0XIAOMAO0/CWU_LED/software/CWU_LED/project/inc/cct_to_cie.h

#ifndef CCT_TO_CIE_H
#define CCT_TO_CIE_H

#define CCT_MIN 2500
#define CCT_MAX 6500

#define CCT_RANGE (CCT_MAX - CCT_MIN)
// This file is used to convert CCT to CIE color space.
// The CCT range is 2500K-6500K.
const float CIE_ARRY[][2] ={
{0.476993298233858,	0.413675289942435}, // 2500k	
{0.476099925127525,	0.413553952226202}, // 2510k	
{0.475210446423188,	0.413428827337877}, // 2520k	
{0.474324856106916,	0.413299979486579}, // 2530k	
{0.473443147918802,	0.413167472190078}, // 2540k	
{0.472565315357245,	0.413031368275923}, // 2550k	
{0.471691351683258,	0.412891729882807}, // 2560k	
{0.470821249924792,	0.412748618462133}, // 2570k	
{0.469955002881062,	0.412602094779799}, // 2580k	
{0.469092603126886,	0.412452218918178}, // 2590k	
{0.468234043017033,	0.412299050278290}, // 2600k	
{0.467379314690560,	0.412142647582159}, // 2610k	
{0.466528410075157,	0.411983068875347}, // 2620k	
{0.465681320891482,	0.411820371529656}, // 2630k	
{0.464838038657489,	0.411654612245991}, // 2640k	
{0.463998554692746,	0.411485847057383}, // 2650k	
{0.463162860122743,	0.411314131332149}, // 2660k	
{0.462330945883173,	0.411139519777208}, // 2670k	
{0.461502802724214,	0.410962066441520}, // 2680k	
{0.460678421214773,	0.410781824719658}, // 2690k	
{0.459857791746717,	0.410598847355503}, // 2700k	
{0.459040904539081,	0.410413186446054}, // 2710k	
{0.458227749642249,	0.410224893445347}, // 2720k	
{0.457418316942099,	0.410034019168485}, // 2730k	
{0.456612596164132,	0.409840613795755}, // 2740k	
{0.455810576877562,	0.409644726876854}, // 2750k	
{0.455012248499377,	0.409446407335191}, // 2760k	
{0.454217600298360,	0.409245703472280}, // 2770k	
{0.453426621399085,	0.409042662972206}, // 2780k	
{0.452639300785869,	0.408837332906172}, // 2790k	
{0.451855627306685,	0.408629759737106}, // 2800k	
{0.451075589677048,	0.408419989324343}, // 2810k	
{0.450299176483844,	0.408208066928357}, // 2820k	
{0.449526376189136,	0.407994037215556}, // 2830k	
{0.448757177133914,	0.407777944263126}, // 2840k	
{0.447991567541816,	0.407559831563923}, // 2850k	
{0.447229535522791,	0.407339742031414}, // 2860k	
{0.446471069076735,	0.407117718004646}, // 2870k	
{0.445716156097067,	0.406893801253269}, // 2880k	
{0.444964784374273,	0.406668032982576}, // 2890k	
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
};



#endif
