0XIAOMAO0/CWU_LED/software/CWU_LED/project/src/at32f421_int.c

/* add user code begin Header */
/**
  **************************************************************************
  * @file     at32f421_int.c
  * @brief    main interrupt service routines.
  **************************************************************************
  *                       Copyright notice & Disclaimer
  *
  * The software Board Support Package (BSP) that is made available to
  * download from Artery official website is the copyrighted work of Artery.
  * Artery authorizes customers to use, copy, and distribute the BSP
  * software and its related documentation for the purpose of design and
  * development in conjunction with Artery microcontrollers. Use of the
  * software is governed by this copyright notice and the following disclaimer.
  *
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
  **************************************************************************
  */
/* add user code end Header */

/* includes ------------------------------------------------------------------*/
#include "at32f421_int.h"

/* private includes ----------------------------------------------------------*/
/* add user code begin private includes */
#include "at32f421_wk_config.h"
/* add user code end private includes */

/* private typedef -----------------------------------------------------------*/
/* add user code begin private typedef */

/* add user code end private typedef */

/* private define ------------------------------------------------------------*/
/* add user code begin private define */

/* add user code end private define */

/* private macro -------------------------------------------------------------*/
/* add user code begin private macro */

/* add user code end private macro */

/* private variables ---------------------------------------------------------*/
/* add user code begin private variables */

/* add user code end private variables */

/* private function prototypes --------------------------------------------*/
/* add user code begin function prototypes */

/* add user code end function prototypes */

/* private user code ---------------------------------------------------------*/
/* add user code begin 0 */

/* add user code end 0 */

/* external variables ---------------------------------------------------------*/
/* add user code begin external variables */

/* add user code end external variables */

/**
  * @brief  this function handles nmi exception.
  * @param  none
  * @retval none
  */
void NMI_Handler(void)
{
  /* add user code begin NonMaskableInt_IRQ 0 */

  /* add user code end NonMaskableInt_IRQ 0 */

  /* add user code begin NonMaskableInt_IRQ 1 */

  /* add user code end NonMaskableInt_IRQ 1 */
}

/**
  * @brief  this function handles hard fault exception.
  * @param  none
  * @retval none
  */
void HardFault_Handler(void)
{
  /* add user code begin HardFault_IRQ 0 */

  /* add user code end HardFault_IRQ 0 */
  /* go to infinite loop when hard fault exception occurs */
  while (1)
  {
    /* add user code begin W1_HardFault_IRQ 0 */

    /* add user code end W1_HardFault_IRQ 0 */
  }
}

/**
  * @brief  this function handles memory manage exception.
  * @param  none
  * @retval none
  */
void MemManage_Handler(void)
{
  /* add user code begin MemoryManagement_IRQ 0 */

  /* add user code end MemoryManagement_IRQ 0 */
  /* go to infinite loop when memory manage exception occurs */
  while (1)
  {
    /* add user code begin W1_MemoryManagement_IRQ 0 */

    /* add user code end W1_MemoryManagement_IRQ 0 */
  }
}

/**
  * @brief  this function handles bus fault exception.
  * @param  none
  * @retval none
  */
void BusFault_Handler(void)
{
  /* add user code begin BusFault_IRQ 0 */

  /* add user code end BusFault_IRQ 0 */
  /* go to infinite loop when bus fault exception occurs */
  while (1)
  {
    /* add user code begin W1_BusFault_IRQ 0 */

    /* add user code end W1_BusFault_IRQ 0 */
  }
}

/**
  * @brief  this function handles usage fault exception.
  * @param  none
  * @retval none
  */
void UsageFault_Handler(void)
{
  /* add user code begin UsageFault_IRQ 0 */

  /* add user code end UsageFault_IRQ 0 */
  /* go to infinite loop when usage fault exception occurs */
  while (1)
  {
    /* add user code begin W1_UsageFault_IRQ 0 */

    /* add user code end W1_UsageFault_IRQ 0 */
  }
}

/**
  * @brief  this function handles svcall exception.
  * @param  none
  * @retval none
  */
void SVC_Handler(void)
{
  /* add user code begin SVCall_IRQ 0 */

  /* add user code end SVCall_IRQ 0 */
  /* add user code begin SVCall_IRQ 1 */

  /* add user code end SVCall_IRQ 1 */
}

/**
  * @brief  this function handles debug monitor exception.
  * @param  none
  * @retval none
  */
void DebugMon_Handler(void)
{
  /* add user code begin DebugMonitor_IRQ 0 */

  /* add user code end DebugMonitor_IRQ 0 */
  /* add user code begin DebugMonitor_IRQ 1 */

  /* add user code end DebugMonitor_IRQ 1 */
}

/**
  * @brief  this function handles pendsv_handler exception.
  * @param  none
  * @retval none
  */
void PendSV_Handler(void)
{
  /* add user code begin PendSV_IRQ 0 */

  /* add user code end PendSV_IRQ 0 */
  /* add user code begin PendSV_IRQ 1 */

  /* add user code end PendSV_IRQ 1 */
}

/**
  * @brief  this function handles systick handler.
  * @param  none
  * @retval none
  */
void SysTick_Handler(void)
{
  /* add user code begin SysTick_IRQ 0 */

  /* add user code end SysTick_IRQ 0 */


  /* add user code begin SysTick_IRQ 1 */

  /* add user code end SysTick_IRQ 1 */
}

/**
  * @brief  this function handles EXINT Line 15 ~ 4 handler.
  * @param  none
  * @retval none
  */
void EXINT15_4_IRQHandler(void)
{
  /* add user code begin EXINT15_4_IRQ 0 */
  if(exint_flag_get(EXINT_LINE_11) != RESET)
  {
    static uint8_t key_flag = 0;
    uint16_t timeout = 500;
    wk_delay_ms(100);
    while ((gpio_input_data_bit_read(KEY_GPIO_PORT, KEY_PIN) == RESET) && timeout)
    {
      wk_delay_ms(1);
      timeout --;
    }
    exint_flag_clear(EXINT_LINE_11);		
    if(timeout == 0) return ;
    key_flag = !key_flag;
    cwu_mode_set(key_flag);
  }
  /* add user code end EXINT15_4_IRQ 0 */
  /* add user code begin EXINT15_4_IRQ 1 */

  /* add user code end EXINT15_4_IRQ 1 */
}

/**
  * @brief  this function handles DMA1 Channel 1 handler.
  * @param  none
  * @retval none
  */
void DMA1_Channel1_IRQHandler(void)
{
  /* add user code begin DMA1_Channel1_IRQ 0 */
  if(dma_flag_get(DMA1_FDT1_FLAG) != RESET)
  {  
    cwu_adc_push(adc_buff);
    dma_flag_clear(DMA1_FDT1_FLAG);
  }
  /* add user code end DMA1_Channel1_IRQ 0 */
  /* add user code begin DMA1_Channel1_IRQ 1 */

  /* add user code end DMA1_Channel1_IRQ 1 */
}

/* add user code begin 1 */

/* add user code end 1 */
